RebeccaRGB/lisakeys/lisakeys/config.h

#ifndef CONFIG_H
#define CONFIG_H

#define LK_LED 13

// See also lisakeysconfig.h.

#define LK_SW_HOST_CLIENT_MODE 5
#define LK_SW_SERIAL_USB_MODE  4
#define LK_SW_SETTING_1        3
#define LK_SW_SETTING_2        2
#define LK_SW_SETTING_3        1
#define LK_SW_SETTING_4        0

// See also keypadconfig.h.

// See also usbkeysconfig.h.

#endif
